Pakequis/Clock_PiW/hardware/clock_sch.kicad_sch

## KiCad design hardware/clock_sch.kicad_sch (2024-12-28)

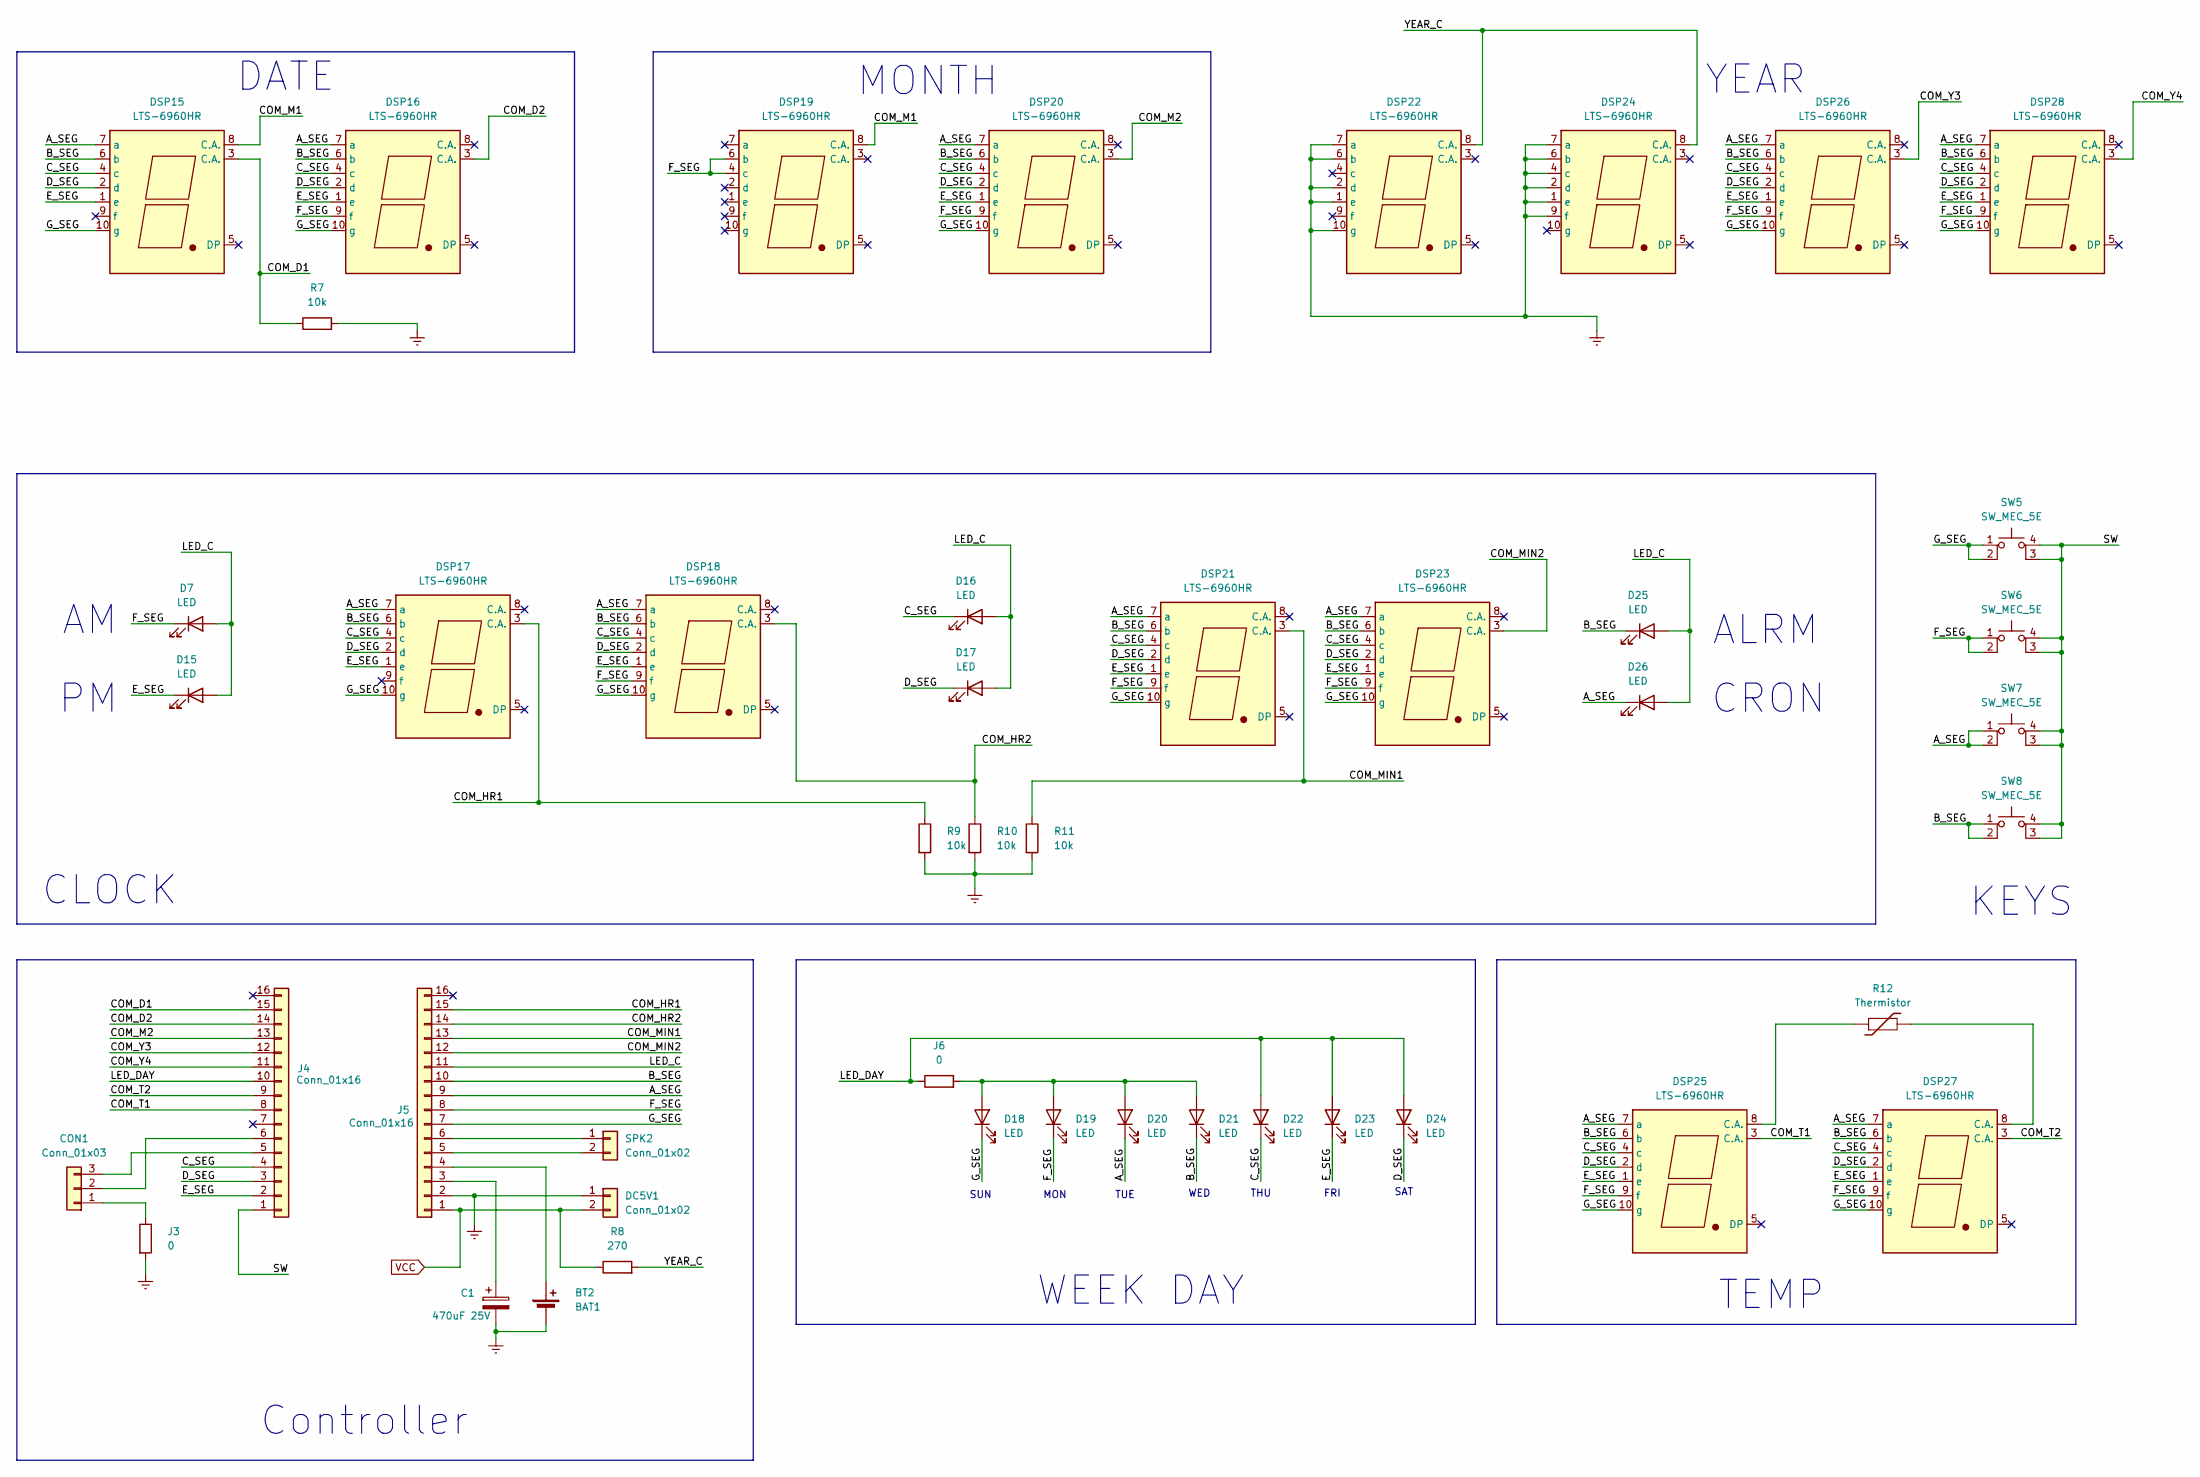
[picture p14: schematic clock_sch.kicad_sch]

Parts:
BT2: BAT1
C1: 470uF 25V
CON1: Conn_01x03
D7, D15, D16, D17, D18, D19, D20, D21, D22, D23, D24, D25, D26: LED
DC5V1: Conn_01x02
DSP15, DSP16, DSP17, DSP18, DSP19, DSP20, DSP21, DSP22, DSP23, DSP24, DSP25, DSP26, DSP27, DSP28: LTS-6960HR; 7SegmentLED_LTS6760_LTS6780
J3, J6: 0
J4, J5: Conn_01x16
R7, R9, R10, R11: 10k
R8: 270
R12: Thermistor
SPK2: Conn_01x02
SW5, SW6, SW7, SW8: SW_MEC_5E

Connections:
A_SEG: D20.1 (K), D26.1 (K), DSP15.7 (a), DSP16.7 (a), DSP17.7 (a), DSP18.7 (a), DSP20.7 (a), DSP21.7 (a), DSP23.7 (a), DSP25.7 (a), DSP26.7 (a), DSP27.7 (a), DSP28.7 (a), J5.9, SW7.1, SW7.2
B_SEG: D21.1 (K), D25.1 (K), DSP15.6 (b), DSP16.6 (b), DSP17.6 (b), DSP18.6 (b), DSP20.6 (b), DSP21.6 (b), DSP23.6 (b), DSP25.6 (b), DSP26.6 (b), DSP27.6 (b), DSP28.6 (b), J5.10, SW8.1, SW8.2
COM_D1: DSP15.3 (C.A.), J4.15, R7.1
COM_D2: DSP16.3 (C.A.), J4.14
COM_HR1: DSP17.3 (C.A.), J5.15, R9.1
COM_HR2: DSP18.3 (C.A.), J5.14, R10.1
COM_M1: DSP15.8 (C.A.), DSP19.8 (C.A.)
COM_M2: DSP20.3 (C.A.), J4.13
COM_MIN1: DSP21.3 (C.A.), J5.13, R11.1
COM_MIN2: DSP23.3 (C.A.), J5.12
COM_T1: DSP25.3 (C.A.), J4.8
COM_T2: DSP27.3 (C.A.), J4.9
COM_Y3: DSP26.3 (C.A.), J4.12
COM_Y4: DSP28.3 (C.A.), J4.11
C_SEG: D16.1 (K), D22.1 (K), DSP15.4 (c), DSP16.4 (c), DSP17.4 (c), DSP18.4 (c), DSP20.4 (c), DSP21.4 (c), DSP23.4 (c), DSP25.4 (c), DSP26.4 (c), DSP27.4 (c), DSP28.4 (c), J4.4
D_SEG: D17.1 (K), D24.1 (K), DSP15.2 (d), DSP16.2 (d), DSP17.2 (d), DSP18.2 (d), DSP20.2 (d), DSP21.2 (d), DSP23.2 (d), DSP25.2 (d), DSP26.2 (d), DSP27.2 (d), DSP28.2 (d), J4.3
E_SEG: D15.1 (K), D23.1 (K), DSP15.1 (e), DSP16.1 (e), DSP17.1 (e), DSP18.1 (e), DSP20.1 (e), DSP21.1 (e), DSP23.1 (e), DSP25.1 (e), DSP26.1 (e), DSP27.1 (e), DSP28.1 (e), J4.2
F_SEG: D7.1 (K), D19.1 (K), DSP16.9 (f), DSP18.9 (f), DSP19.4 (c), DSP19.6 (b), DSP20.9 (f), DSP21.9 (f), DSP23.9 (f), DSP25.9 (f), DSP26.9 (f), DSP27.9 (f), DSP28.9 (f), J5.8, SW6.1, SW6.2
GNDREF: BT2.2 (-), C1.2, DC5V1.1, DSP22.1 (e), DSP22.2 (d), DSP22.6 (b), DSP22.7 (a), DSP22.10 (g), DSP24.1 (e), DSP24.2 (d), DSP24.4 (c), DSP24.6 (b), DSP24.7 (a), DSP24.9 (f), J3.2, J5.2, R7.2, R9.2, R10.2, R11.2
G_SEG: D18.1 (K), DSP15.10 (g), DSP16.10 (g), DSP17.10 (g), DSP18.10 (g), DSP20.10 (g), DSP21.10 (g), DSP23.10 (g), DSP25.10 (g), DSP26.10 (g), DSP27.10 (g), DSP28.10 (g), J5.7, SW5.1, SW5.2
LED_C: D7.2 (A), D15.2 (A), D16.2 (A), D17.2 (A), D25.2 (A), D26.2 (A), J5.11
LED_DAY: D22.2 (A), D23.2 (A), D24.2 (A), J4.10, J6.1
unnamed: BT2.1 (+), J5.4
unnamed: C1.1, J5.3
unnamed: CON1.1, J3.1
unnamed: CON1.2, J4.6
unnamed: CON1.3, J4.5
unnamed: D18.2 (A), D19.2 (A), D20.2 (A), D21.2 (A), J6.2
unnamed: DSP25.8 (C.A.), R12.1
unnamed: DSP27.8 (C.A.), R12.2
unnamed: J5.5, SPK2.2
unnamed: J5.6, SPK2.1
SW: J4.1, SW5.3 (K), SW5.4 (A), SW6.3 (K), SW6.4 (A), SW7.3 (K), SW7.4 (A), SW8.3 (K), SW8.4 (A)
VCC: DC5V1.2, J5.1, R8.1
YEAR_C: DSP22.8 (C.A.), DSP24.8 (C.A.), R8.2

Notes on the sheet:
ALRM
SAT
MONTH
YEAR
FRI
CLOCK
TEMP
CRON
DATE
TUE
SUN
THU
KEYS
WEEK DAY
WED
MON
Controller
