Pakequis/Clock_PiW/hardware/conn_sch.kicad_sch

## KiCad design hardware/conn_sch.kicad_sch (2024-12-28)

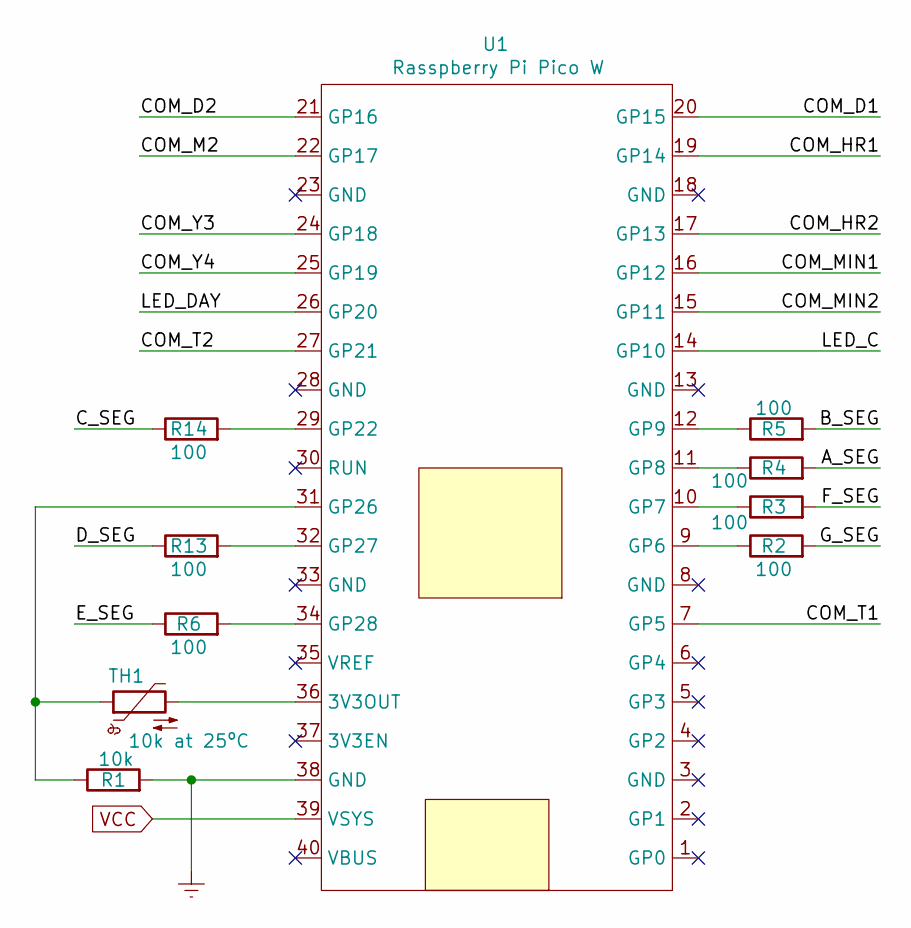
[picture p15: schematic conn_sch.kicad_sch]

Parts:
R1: 10k
R2, R3, R4, R5, R6, R13, R14: 100
TH1: 10k at 25ºC
U1: Rasspberry Pi Pico W

Connections:
A_SEG: R4.2
B_SEG: R5.2
COM_D1: U1.20 (GP15)
COM_D2: U1.21 (GP16)
COM_HR1: U1.19 (GP14)
COM_HR2: U1.17 (GP13)
COM_M2: U1.22 (GP17)
COM_MIN1: U1.16 (GP12)
COM_MIN2: U1.15 (GP11)
COM_T1: U1.7 (GP5)
COM_T2: U1.27 (GP21)
COM_Y3: U1.24 (GP18)
COM_Y4: U1.25 (GP19)
C_SEG: R14.1
D_SEG: R13.1
E_SEG: R6.1
F_SEG: R3.2
GNDREF: R1.2, U1.38 (GND)
G_SEG: R2.2
LED_C: U1.14 (GP10)
LED_DAY: U1.26 (GP20)
unnamed: R1.1, TH1.1, U1.31 (GP26)
unnamed: R2.1, U1.9 (GP6)
unnamed: R3.1, U1.10 (GP7)
unnamed: R4.1, U1.11 (GP8)
unnamed: R5.1, U1.12 (GP9)
unnamed: R6.2, U1.34 (GP28)
unnamed: R13.2, U1.32 (GP27)
unnamed: R14.2, U1.29 (GP22)
unnamed: TH1.2, U1.36 (3V3OUT)
VCC: U1.39 (VSYS)
